UzixLS/pc-kharon-386/images/2.webp

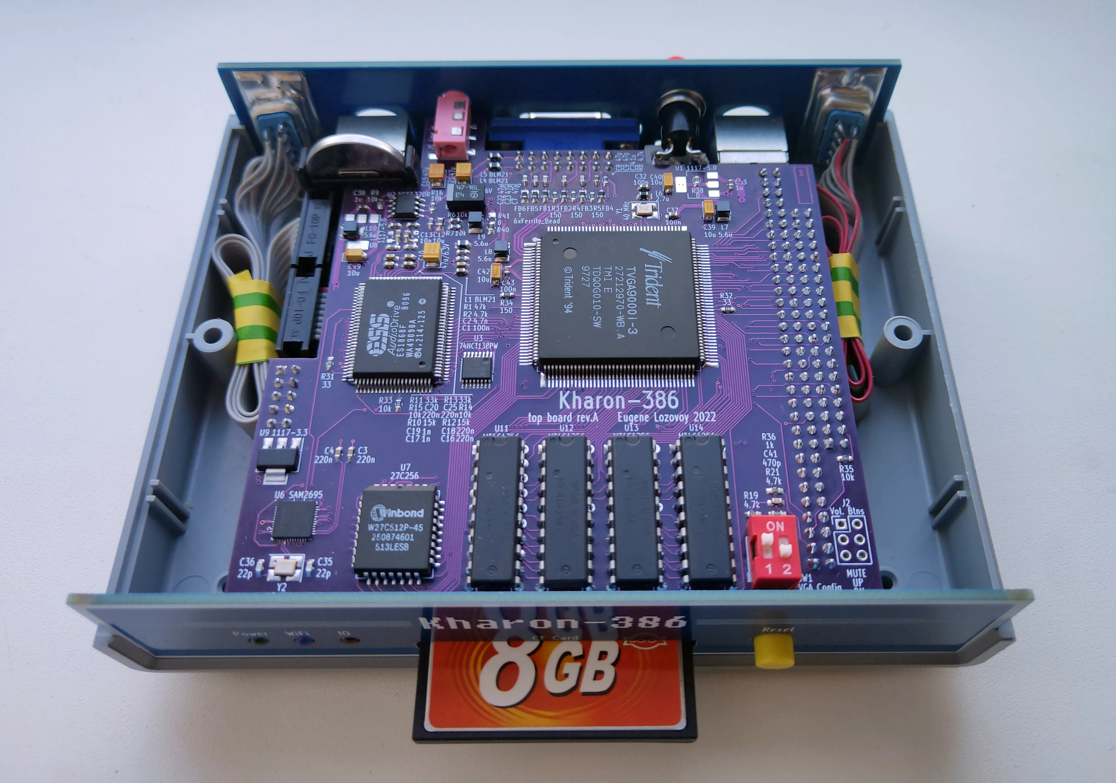
images/2.webp
