UzixLS/pc-kharon-386/images/4.webp

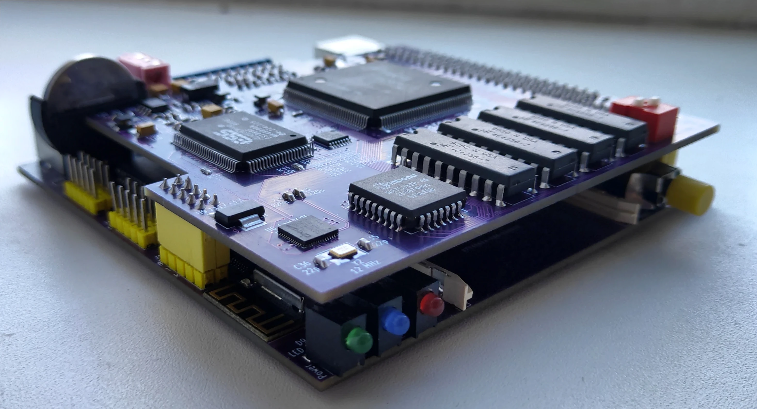
images/4.webp
